ARTS-Laboratory/In-situ-monitoring-of-powder-bed-fusion-additive-manufacturing/system_development/Uru/Triton2 EVS 0.3MP (IMX637) - EventCamera_files/Arena-SDK-Win-short.jpg

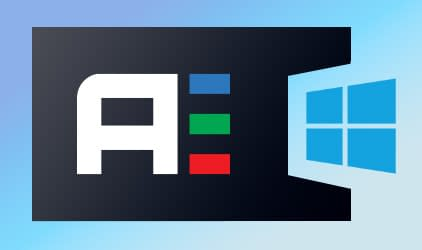
system_development/Uru/Triton2 EVS 0.3MP (IMX637) - EventCamera_files/Arena-SDK-Win-short.jpg
