ARTS-Laboratory/In-situ-monitoring-of-powder-bed-fusion-additive-manufacturing/system_development/Uru/Triton2 EVS 0.3MP (IMX637) - EventCamera_files/Triton2-camera-top-and-bottom-C-mount-2.jpg

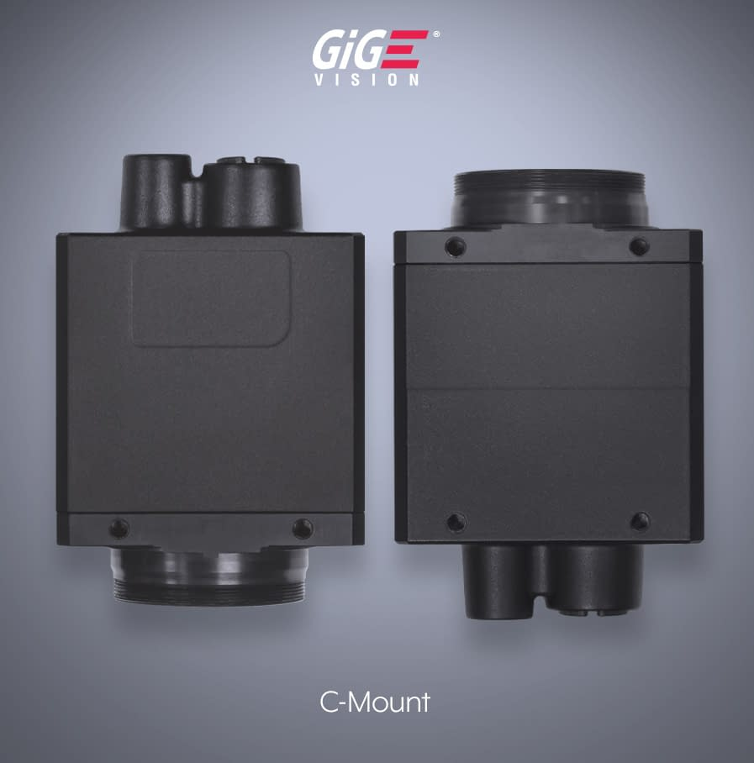
system_development/Uru/Triton2 EVS 0.3MP (IMX637) - EventCamera_files/Triton2-camera-top-and-bottom-C-mount-2.jpg
