ARTS-Laboratory/In-situ-monitoring-of-powder-bed-fusion-additive-manufacturing/system_development/Uru/Triton2 EVS 0.3MP (IMX637) - EventCamera_files/Triton2-EVS-IMX636-IMX637-Prophesee-Event-sensor-1.jpg

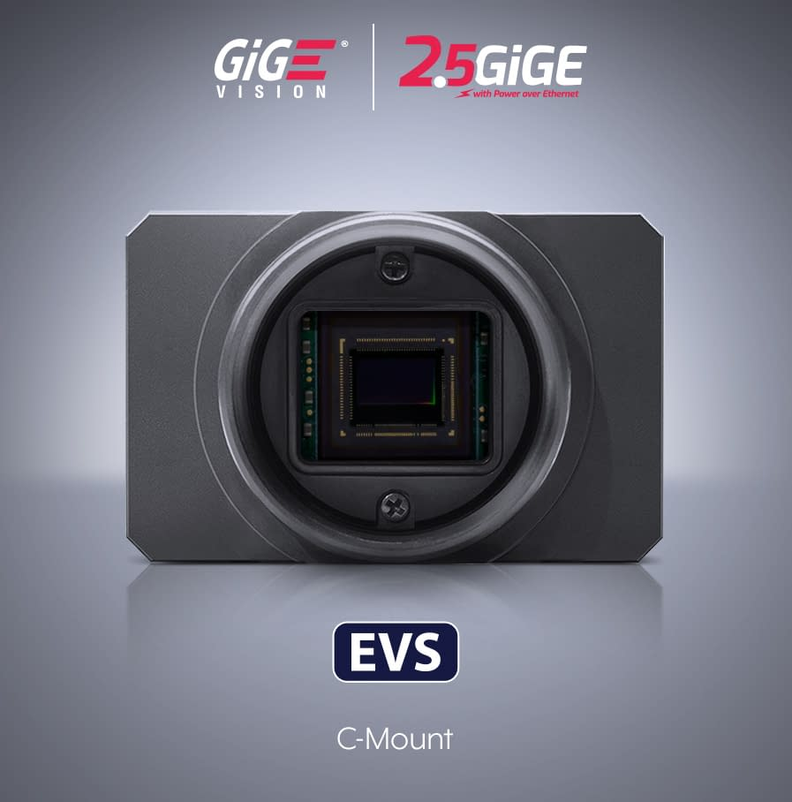
system_development/Uru/Triton2 EVS 0.3MP (IMX637) - EventCamera_files/Triton2-EVS-IMX636-IMX637-Prophesee-Event-sensor-1.jpg
