ARTS-Laboratory/In-situ-monitoring-of-powder-bed-fusion-additive-manufacturing/system_development/Orichalcum/v0.3/step files/Access Cap.stp

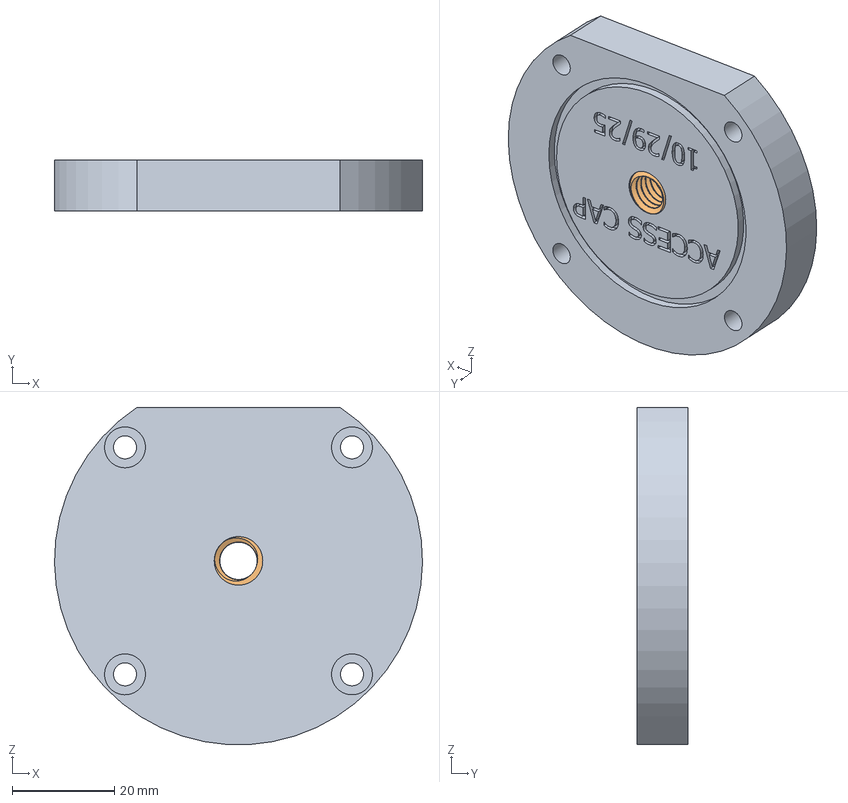
[picture p27: CAD file, 2026-01-07]
system_development/Orichalcum/v0.3/step files/Access Cap.stp
72.0 x 10.0 x 65.9 mm
