ARTS-Laboratory/In-situ-monitoring-of-powder-bed-fusion-additive-manufacturing/system_development/Adamant/v0.2/hardware_development/STEP Files/shape-circle.stl

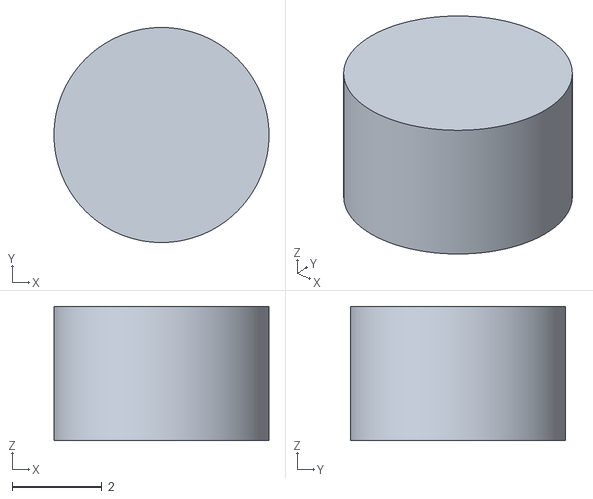
[picture p29: CAD file, 2026-03-04]
system_development/Adamant/v0.2/hardware_development/STEP Files/shape-circle.stl
4.80 x 4.80 x 3.00
