ARTS-Laboratory/In-situ-monitoring-of-powder-bed-fusion-additive-manufacturing/system_development/Mithril/v0.4/hardware_design/STEP Files/SealedGlassRing.stp

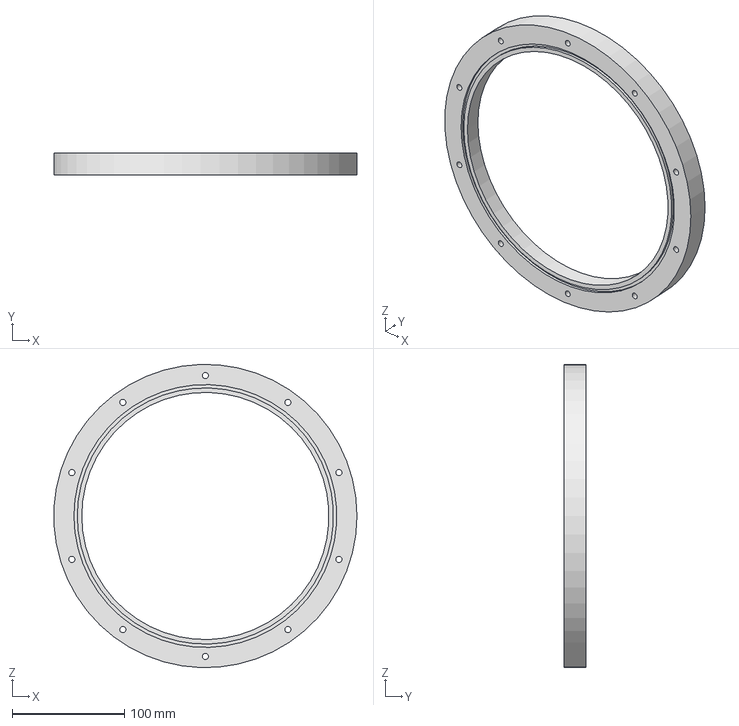
[picture p30: CAD file, 2026-02-27]
system_development/Mithril/v0.4/hardware_design/STEP Files/SealedGlassRing.stp
269.7 x 20.0 x 269.9 mm
