ARTS-Laboratory/In-situ-monitoring-of-powder-bed-fusion-additive-manufacturing/system_development/Orichalcum/v0.3/step files/Cylinder Housing Base.stp

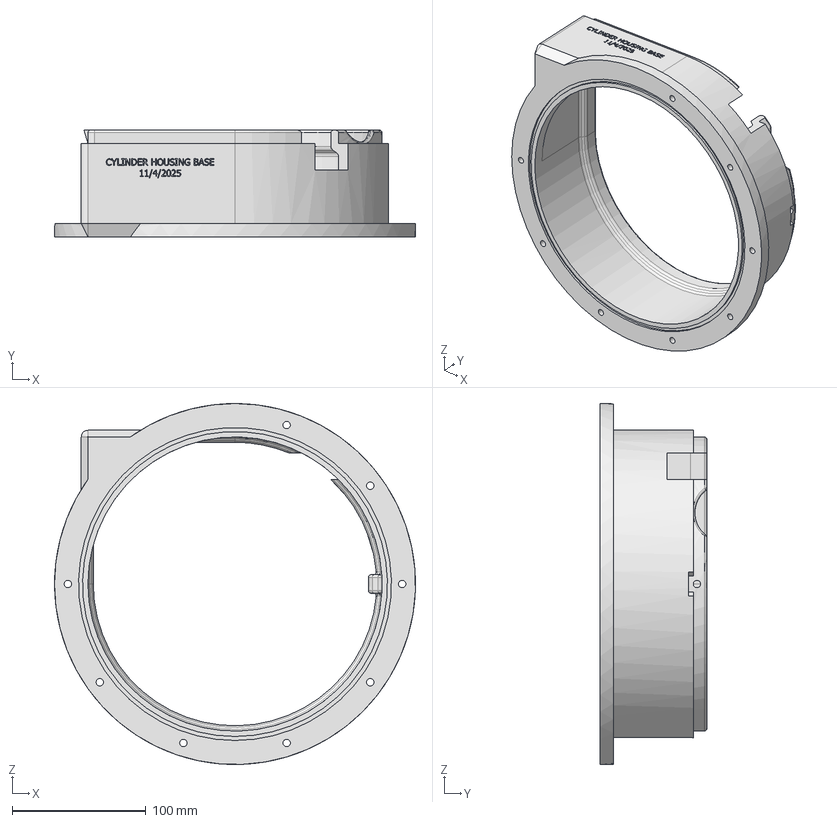
[picture p31: CAD file, 2026-01-07]
system_development/Orichalcum/v0.3/step files/Cylinder Housing Base.stp
270.0 x 80.0 x 270.0 mm
