ARTS-Laboratory/In-situ-monitoring-of-powder-bed-fusion-additive-manufacturing/system_development/Mithril/v0.4/hardware_design/STEP Files/Camera Cylinder Housing - Red Lights Test.stp

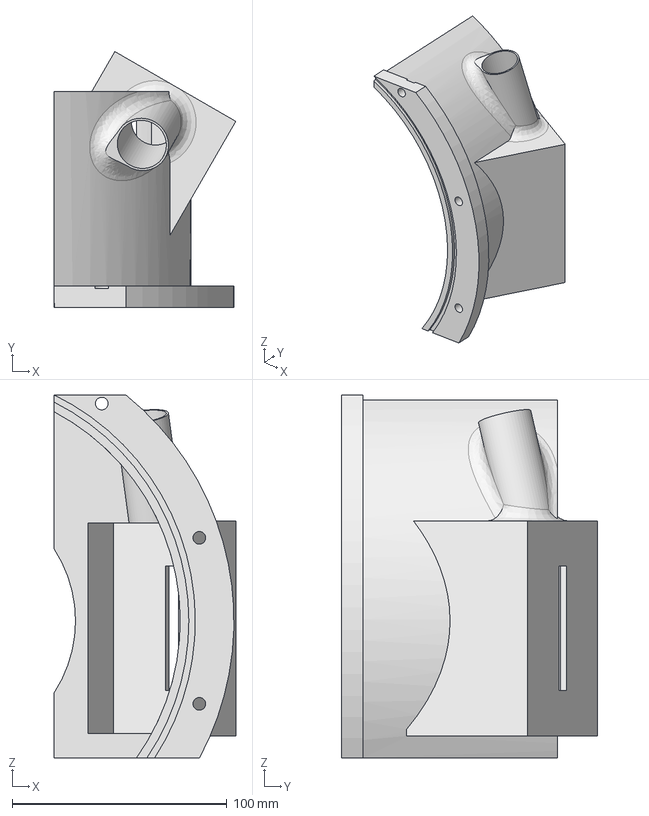
[picture p34: CAD file, 2026-02-27]
system_development/Mithril/v0.4/hardware_design/STEP Files/Camera Cylinder Housing - Red Lights Test.stp
84.5 x 119.1 x 169.0 mm
