ARTS-Laboratory/In-situ-monitoring-of-powder-bed-fusion-additive-manufacturing/system_development/Orichalcum/v0.3/step files/Wire Passthrough Resin Plug.stp

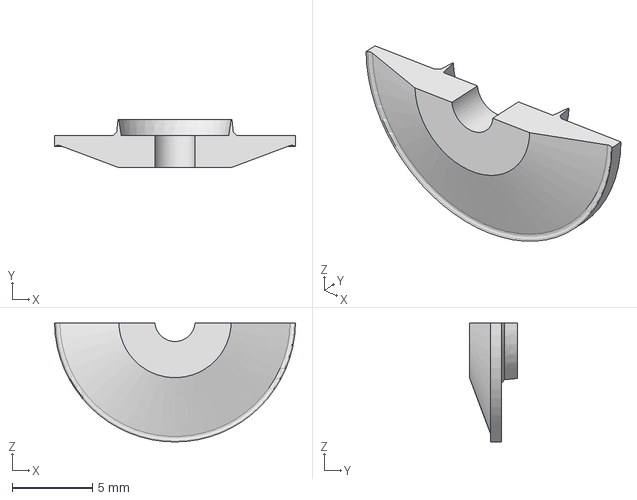
[picture p35: CAD file, 2026-01-07]
system_development/Orichalcum/v0.3/step files/Wire Passthrough Resin Plug.stp
15.0 x 3.00 x 7.40 mm
