ARTS-Laboratory/In-situ-monitoring-of-powder-bed-fusion-additive-manufacturing/accessories/Battery Holder/STEP files/Shield.stp

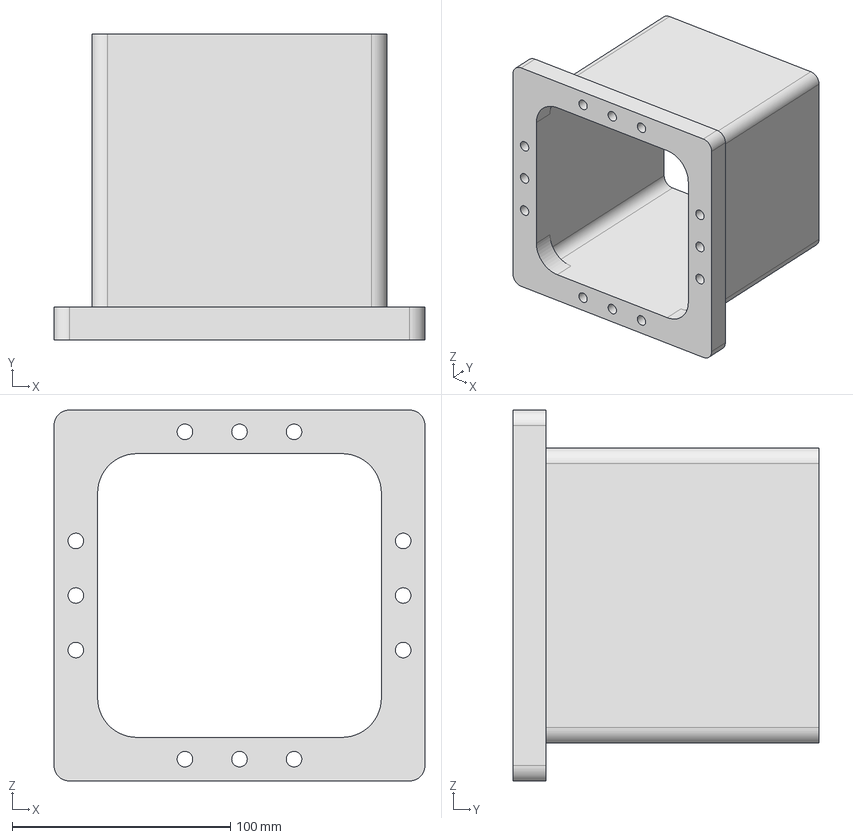
[picture p36: CAD file, 2026-01-07]
accessories/Battery Holder/STEP files/Shield.stp
170.0 x 140.0 x 170.0 mm
