ARTS-Laboratory/In-situ-monitoring-of-powder-bed-fusion-additive-manufacturing/system_development/Adamant/v0.2/hardware_development/STEP Files/Spiral.stl

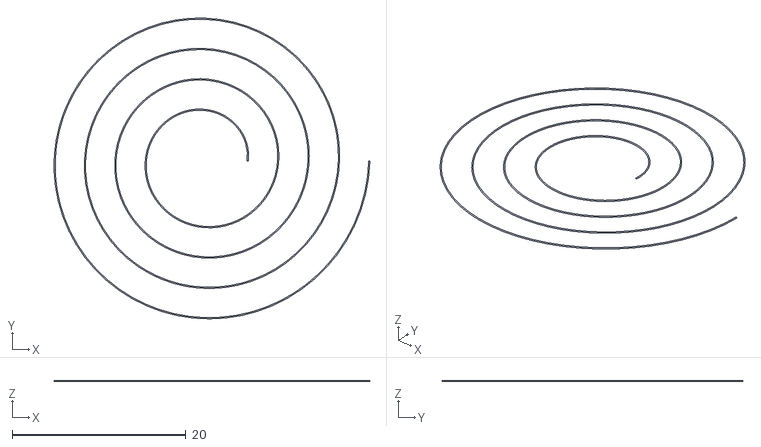
[picture p37: CAD file, 2026-03-04]
system_development/Adamant/v0.2/hardware_development/STEP Files/Spiral.stl
36.4 x 34.6 x 0.148
