ARTS-Laboratory/In-situ-monitoring-of-powder-bed-fusion-additive-manufacturing/system_development/Mithril/v0.4/hardware_design/STEP Files/Camera Cylinder Housing - Red Lights.stp

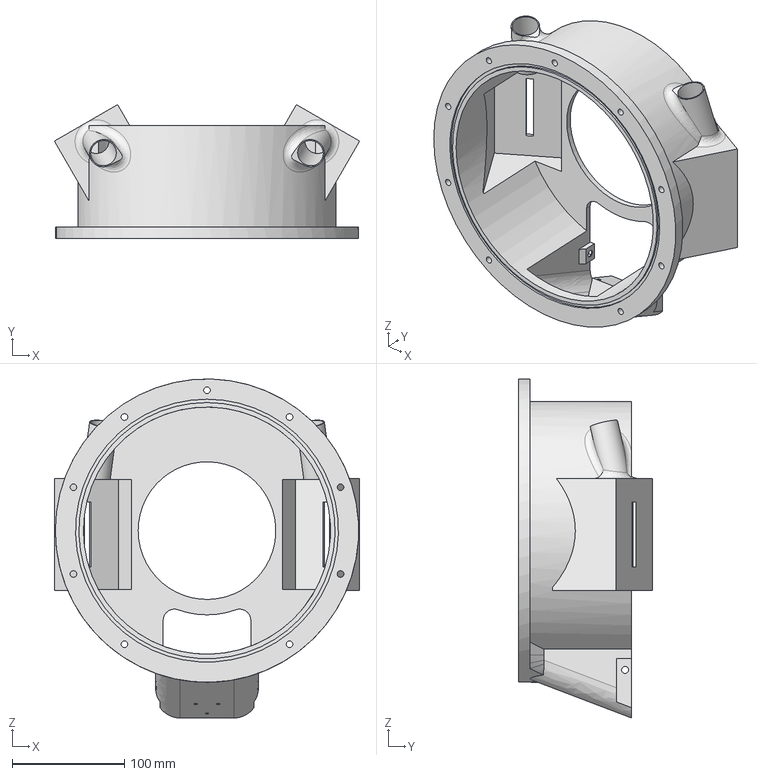
[picture p38: CAD file, 2026-02-27]
system_development/Mithril/v0.4/hardware_design/STEP Files/Camera Cylinder Housing - Red Lights.stp
271.7 x 119.1 x 301.8 mm
