ARTS-Laboratory/In-situ-monitoring-of-powder-bed-fusion-additive-manufacturing/system_development/Orichalcum/v0.3/step files/Cylinder Housing Cap.stp

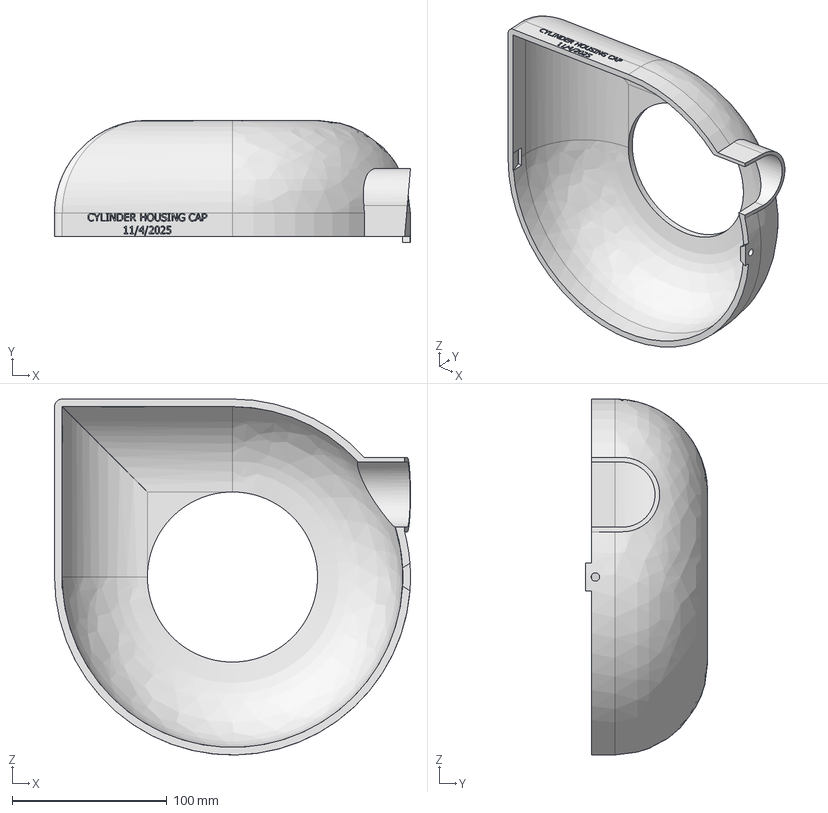
[picture p39: CAD file, 2026-01-07]
system_development/Orichalcum/v0.3/step files/Cylinder Housing Cap.stp
230.0 x 79.0 x 230.0 mm
