ARTS-Laboratory/In-situ-monitoring-of-powder-bed-fusion-additive-manufacturing/system_development/Adamant/v0.2/hardware_development/STEP Files/shape-polygon-6-sides.stl

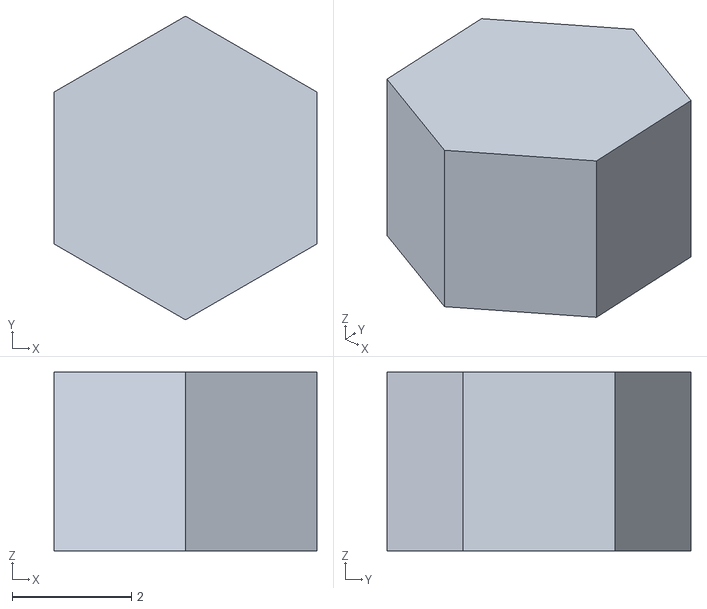
[picture p41: CAD file, 2026-03-04]
system_development/Adamant/v0.2/hardware_development/STEP Files/shape-polygon-6-sides.stl
4.42 x 5.10 x 3.00
