ARTS-Laboratory/In-situ-monitoring-of-powder-bed-fusion-additive-manufacturing/system_development/Mithril/v0.4/hardware_design/STEP Files/Optical Housing.stp

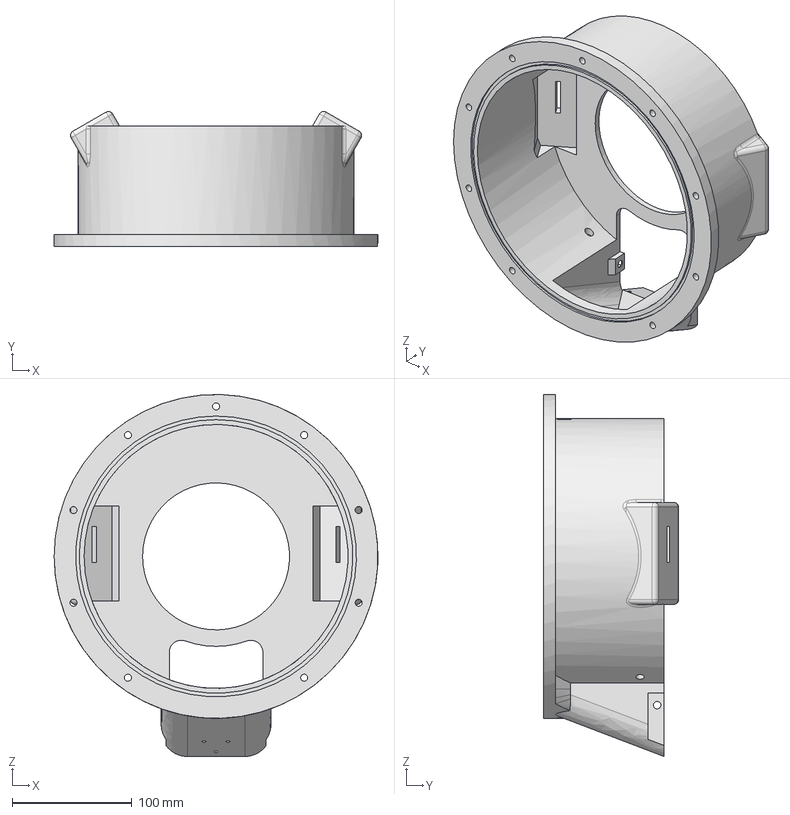
[picture p42: CAD file, 2026-02-12]
system_development/Mithril/v0.4/hardware_design/STEP Files/Optical Housing.stp
269.9 x 112.6 x 301.8 mm
