ARTS-Laboratory/In-situ-monitoring-of-powder-bed-fusion-additive-manufacturing/system_development/Orichalcum/v0.3/step files/holderforcameras.stp

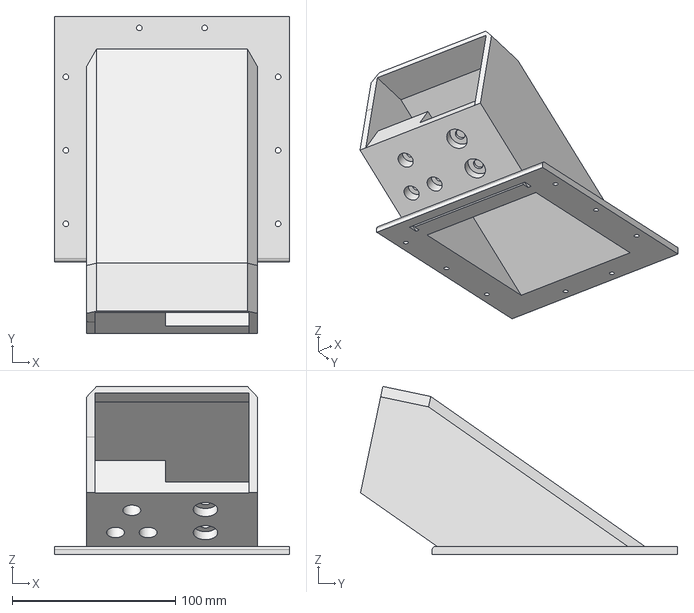
[picture p43: CAD file, 2026-01-07]
system_development/Orichalcum/v0.3/step files/holderforcameras.stp
144.0 x 194.2 x 103.0 mm
