ARTS-Laboratory/In-situ-monitoring-of-powder-bed-fusion-additive-manufacturing/accessories/Battery Holder/STEP files/Battery Holder (Bottom).stp

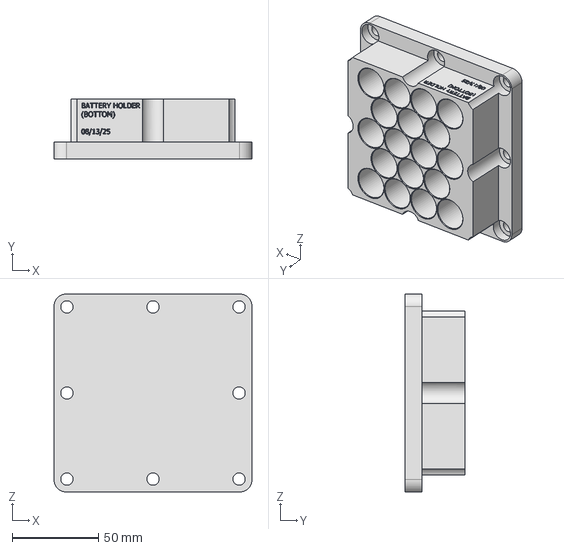
[picture p44: CAD file, 2026-01-07]
accessories/Battery Holder/STEP files/Battery Holder (Bottom).stp
115.0 x 35.0 x 115.0 mm
