ARTS-Laboratory/In-situ-monitoring-of-powder-bed-fusion-additive-manufacturing/system_development/Adamant/v0.2/hardware_development/STEP Files/shape-flower.stl

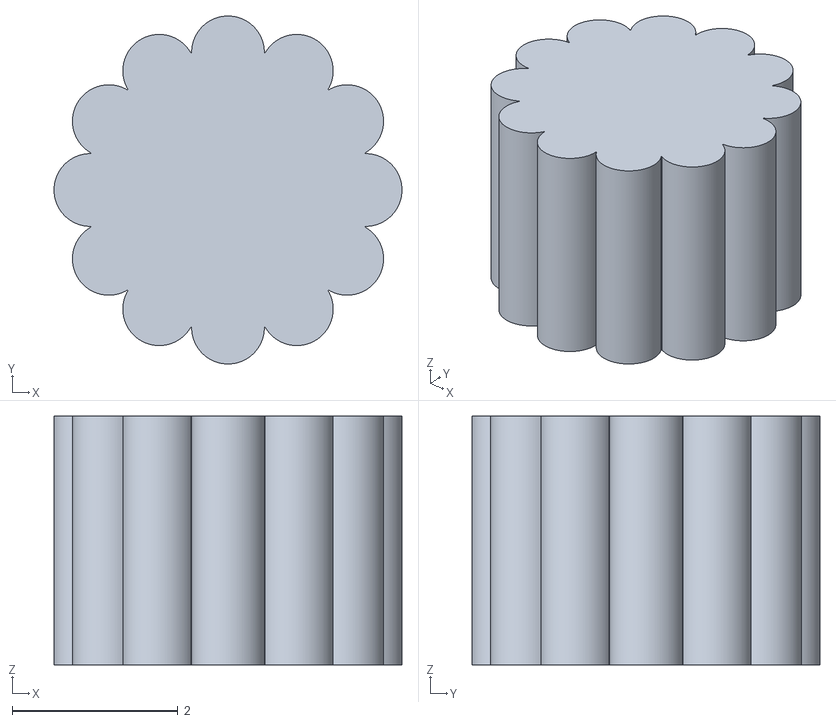
[picture p45: CAD file, 2026-03-04]
system_development/Adamant/v0.2/hardware_development/STEP Files/shape-flower.stl
4.20 x 4.20 x 3.00
