ARTS-Laboratory/In-situ-monitoring-of-powder-bed-fusion-additive-manufacturing/system_development/Mithril/v0.4/hardware_design/STEP Files/Optical Lid.stp

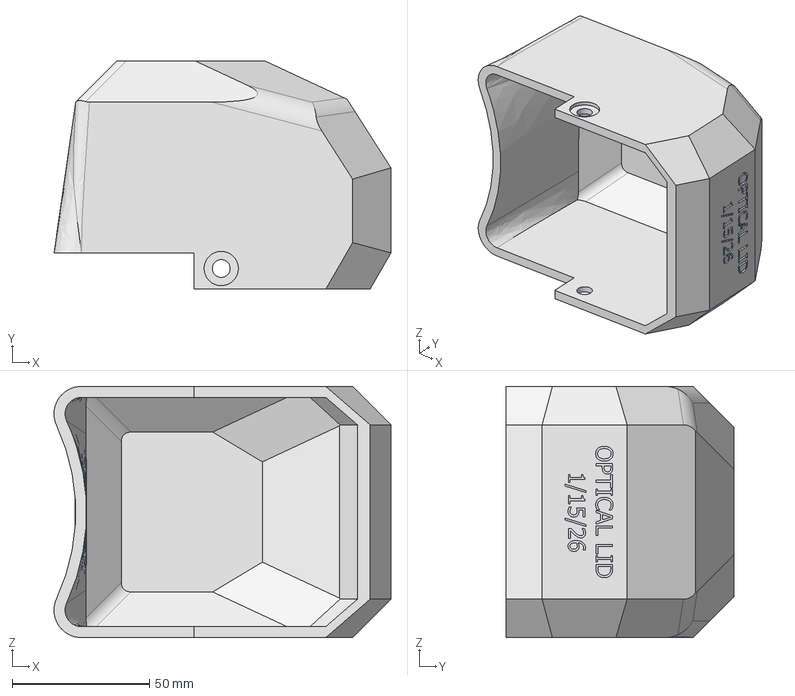
[picture p46: CAD file, 2026-02-12]
system_development/Mithril/v0.4/hardware_design/STEP Files/Optical Lid.stp
122.9 x 83.2 x 91.6 mm
