ARTS-Laboratory/In-situ-monitoring-of-powder-bed-fusion-additive-manufacturing/system_development/Orichalcum/v0.3/step files/LV_Bracket.stp

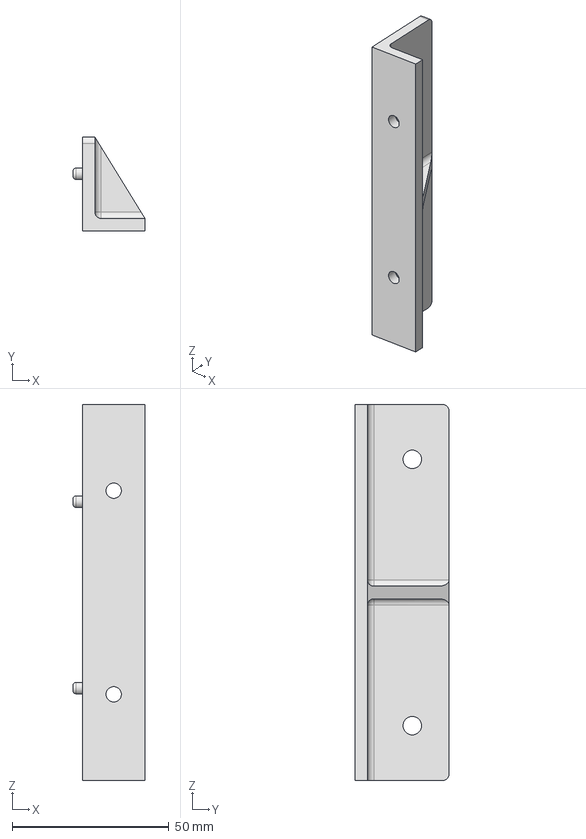
[picture p47: CAD file, 2026-01-07]
system_development/Orichalcum/v0.3/step files/LV_Bracket.stp
23.0 x 30.0 x 120.0 mm
