ARTS-Laboratory/In-situ-monitoring-of-powder-bed-fusion-additive-manufacturing/system_development/Adamant/v0.2/hardware_development/STEP Files/Plastic Clamp Arm.stp

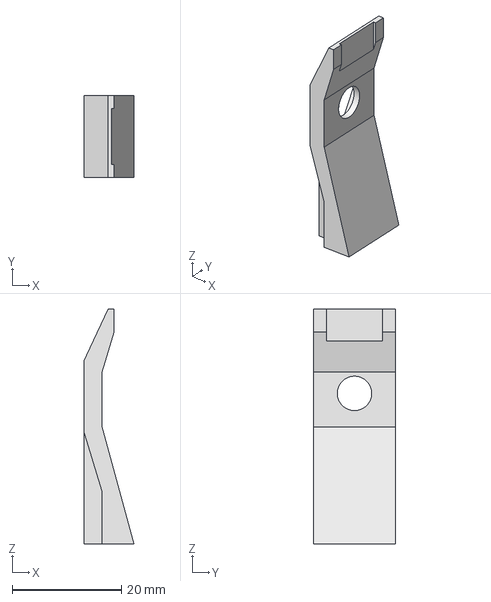
[picture p48: CAD file, 2026-02-27]
system_development/Adamant/v0.2/hardware_development/STEP Files/Plastic Clamp Arm.stp
9.15 x 15.0 x 43.0 mm
