ARTS-Laboratory/In-situ-monitoring-of-powder-bed-fusion-additive-manufacturing/system_development/Mithril/v0.4/hardware_design/STEP Files/Light Box Testing.stp

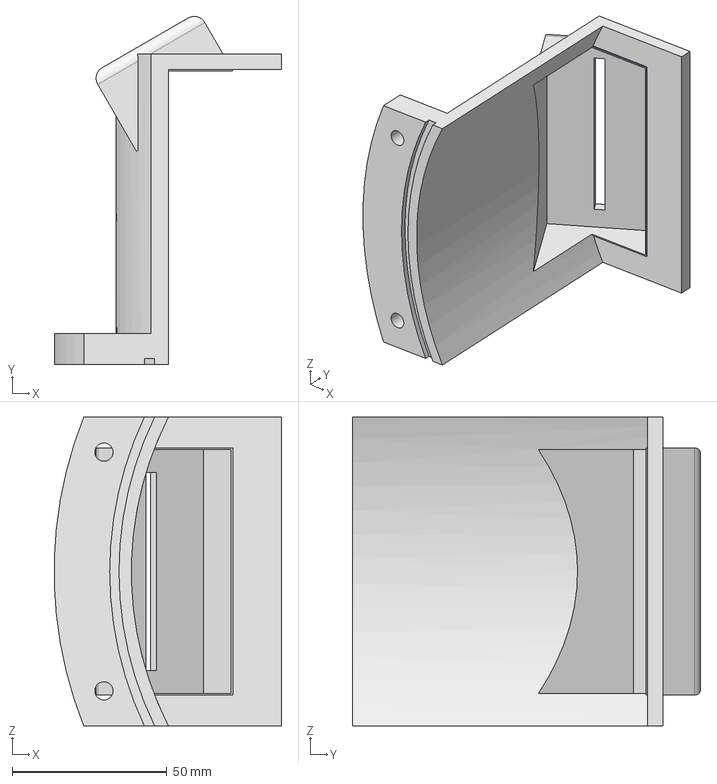
[picture p49: CAD file, 2026-01-07]
system_development/Mithril/v0.4/hardware_design/STEP Files/Light Box Testing.stp
73.6 x 112.6 x 100.0 mm
