ARTS-Laboratory/In-situ-monitoring-of-powder-bed-fusion-additive-manufacturing/system_development/Adamant/v0.2/hardware_development/STEP Files/Cylinder Segment Holder.stp

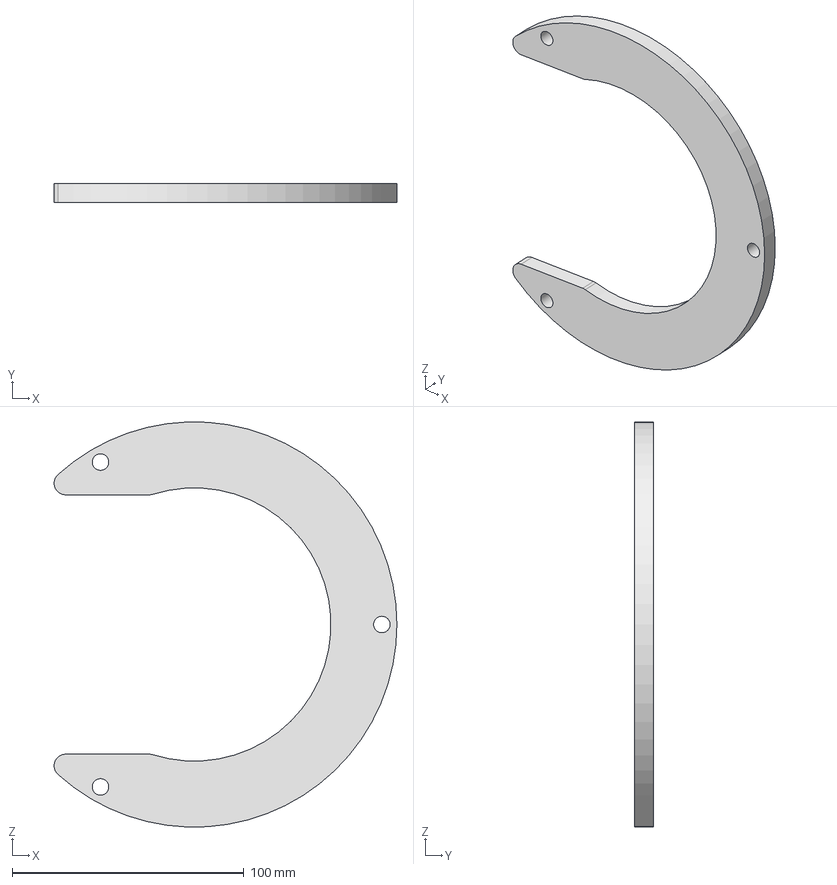
[picture p50: CAD file, 2026-01-07]
system_development/Adamant/v0.2/hardware_development/STEP Files/Cylinder Segment Holder.stp
148.0 x 8.00 x 174.9 mm
