ARTS-Laboratory/In-situ-monitoring-of-powder-bed-fusion-additive-manufacturing/system_development/Adamant/v0.2/hardware_development/STEP Files/New Thermal Lid.stp

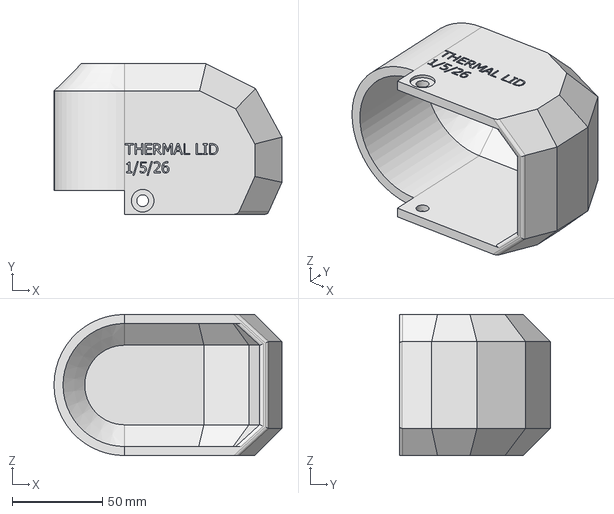
[picture p51: CAD file, 2026-01-07]
system_development/Adamant/v0.2/hardware_development/STEP Files/New Thermal Lid.stp
126.0 x 83.2 x 78.0 mm
