ARTS-Laboratory/In-situ-monitoring-of-powder-bed-fusion-additive-manufacturing/system_development/Adamant/v0.2/hardware_development/STEP Files/lid.3mf

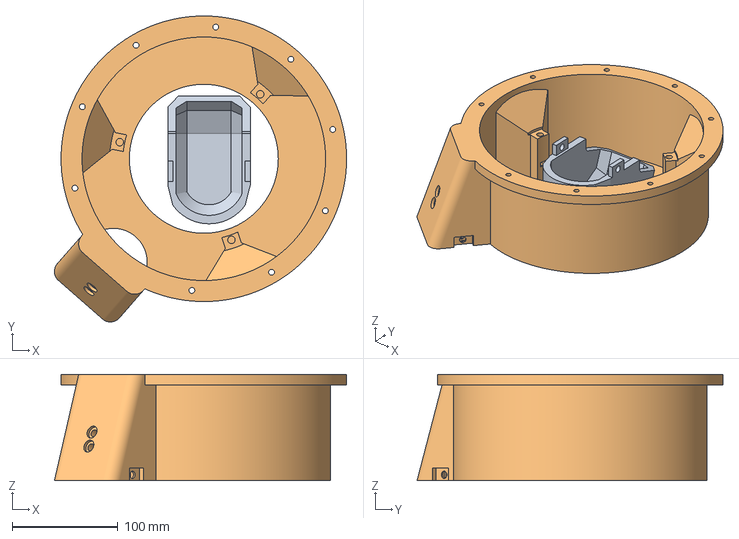
[picture p52: CAD file, 2026-01-07]
system_development/Adamant/v0.2/hardware_development/STEP Files/lid.3mf
276.3 x 289.4 x 100.5 mm
lid.stp
Cylinder Slidey Bit Housing Camera Last.stp
