ARTS-Laboratory/In-situ-monitoring-of-powder-bed-fusion-additive-manufacturing/system_development/Adamant/v0.2/hardware_development/STEP Files/New Thermal Housing.stp

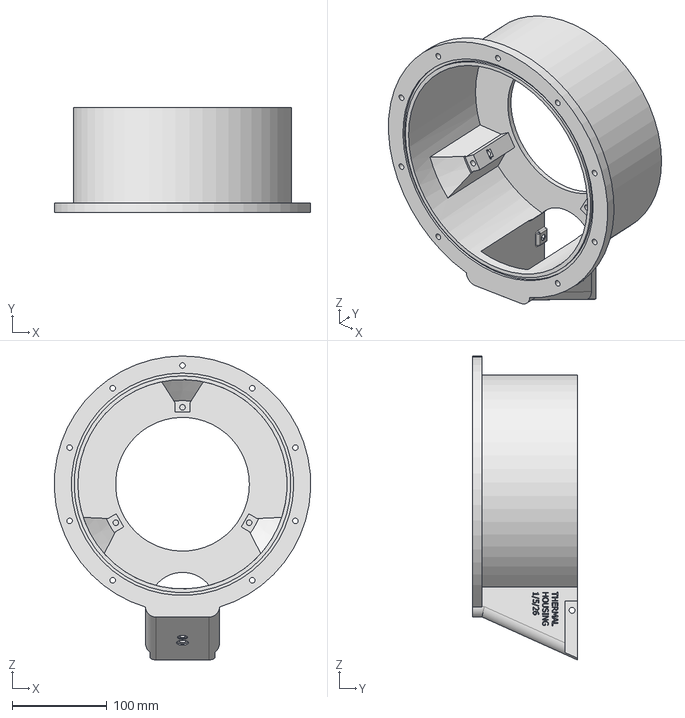
[picture p53: CAD file, 2026-01-07]
system_development/Adamant/v0.2/hardware_development/STEP Files/New Thermal Housing.stp
269.8 x 110.5 x 320.0 mm
