ARTS-Laboratory/In-situ-monitoring-of-powder-bed-fusion-additive-manufacturing/system_development/Adamant/v0.2/hardware_development/STEP Files/Thermal Camera Housing Unit.stp

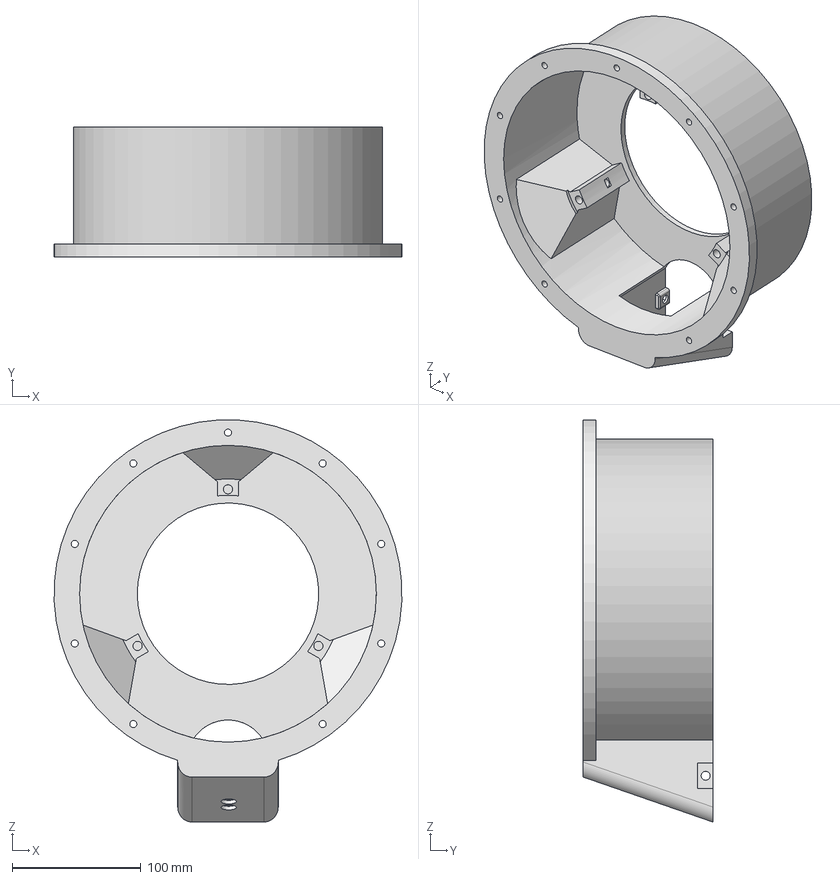
[picture p54: CAD file, 2026-01-07]
system_development/Adamant/v0.2/hardware_development/STEP Files/Thermal Camera Housing Unit.stp
269.7 x 100.5 x 311.9 mm
