ARTS-Laboratory/In-situ-monitoring-of-powder-bed-fusion-additive-manufacturing/system_development/Adamant/v0.2/hardware_development/STEP Files/C .Replace - 10.stp

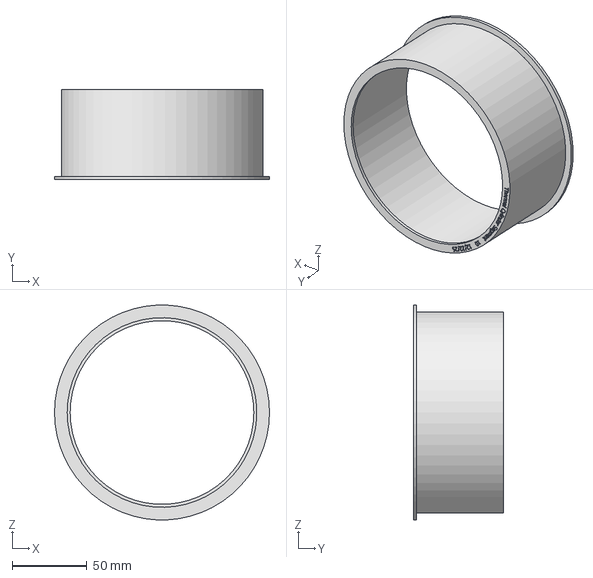
[picture p55: CAD file, 2026-01-07]
system_development/Adamant/v0.2/hardware_development/STEP Files/C .Replace - 10.stp
144.0 x 60.0 x 143.8 mm
