ARTS-Laboratory/In-situ-monitoring-of-powder-bed-fusion-additive-manufacturing/system_development/Adamant/v0.2/hardware_development/STEP Files/Thermal Cover Lid.stp

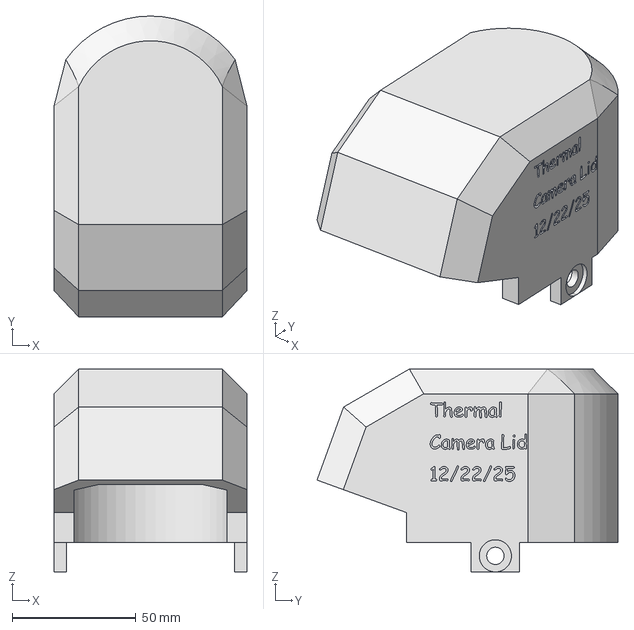
[picture p56: CAD file, 2026-01-07]
system_development/Adamant/v0.2/hardware_development/STEP Files/Thermal Cover Lid.stp
78.0 x 121.6 x 82.0 mm
