ARTS-Laboratory/In-situ-monitoring-of-powder-bed-fusion-additive-manufacturing/system_development/Adamant/v0.2/hardware_development/STEP Files/C .Replace - Face.stp

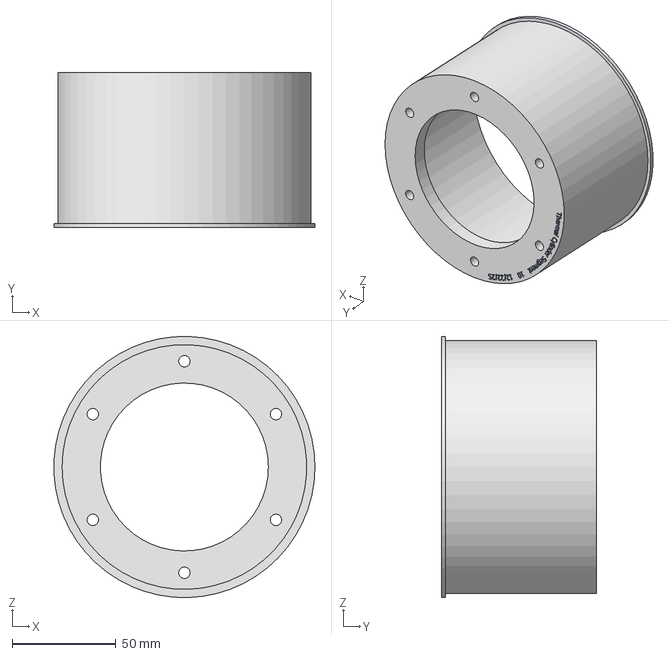
[picture p57: CAD file, 2026-01-07]
system_development/Adamant/v0.2/hardware_development/STEP Files/C .Replace - Face.stp
125.9 x 75.0 x 126.0 mm
