ARTS-Laboratory/In-situ-monitoring-of-powder-bed-fusion-additive-manufacturing/system_development/Adamant/v0.2/hardware_development/STEP Files/Thermal Camera v0.2 LID.stp

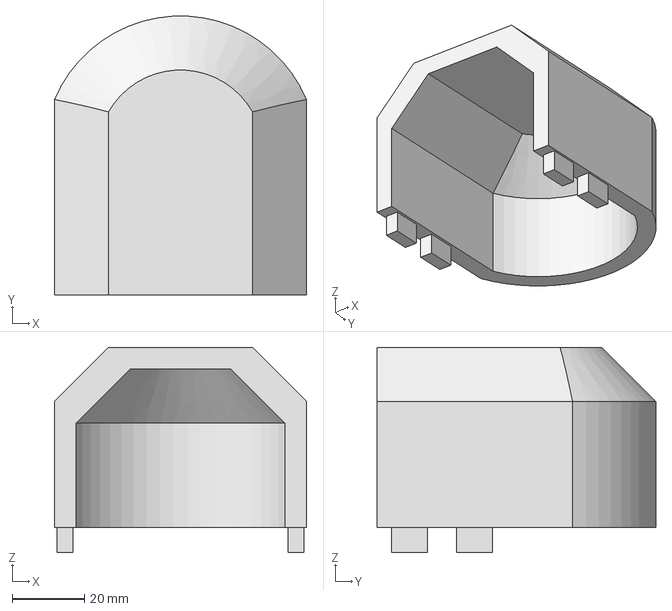
[picture p58: CAD file, 2026-01-07]
system_development/Adamant/v0.2/hardware_development/STEP Files/Thermal Camera v0.2 LID.stp
70.0 x 77.4 x 57.0 mm
